ademuri/colordance-circle/hardware/mechanical/pcb-spacer.stl

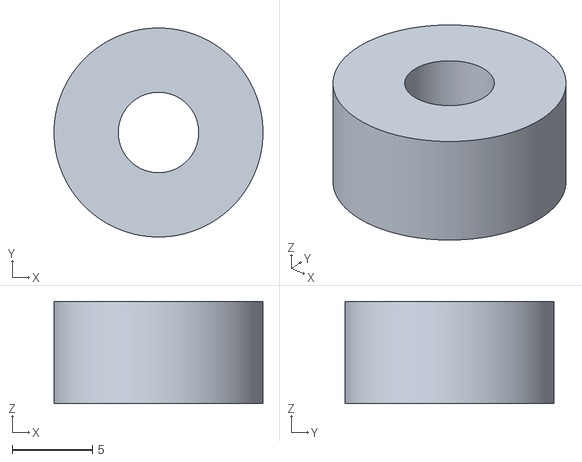
[picture p17: CAD file, 2021-06-12]
hardware/mechanical/pcb-spacer.stl
13.0 x 13.0 x 6.35
