ademuri/colordance-circle/hardware/mechanical/quarter inch washer.stl

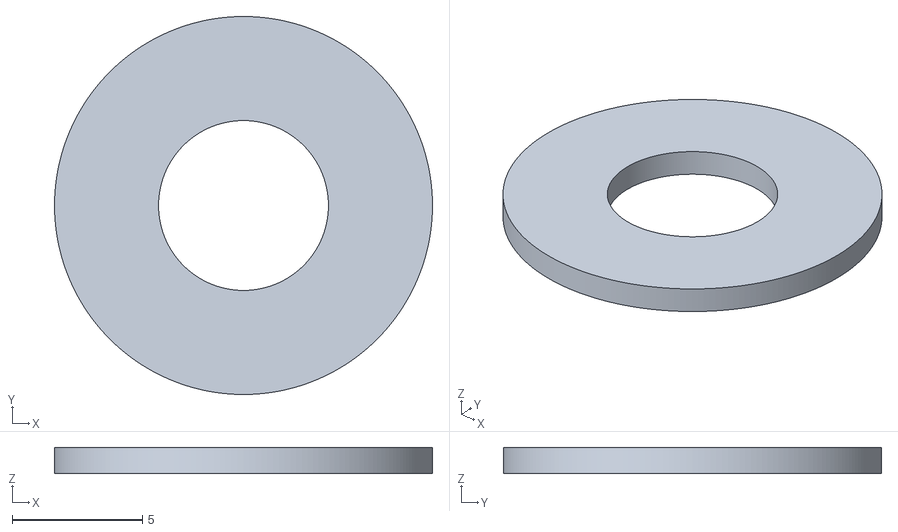
[picture p18: CAD file, 2021-09-08]
hardware/mechanical/quarter inch washer.stl
14.5 x 14.5 x 1.00
