ademuri/colordance-circle/hardware/buttons/circle-small/ref/circle-small.pdf

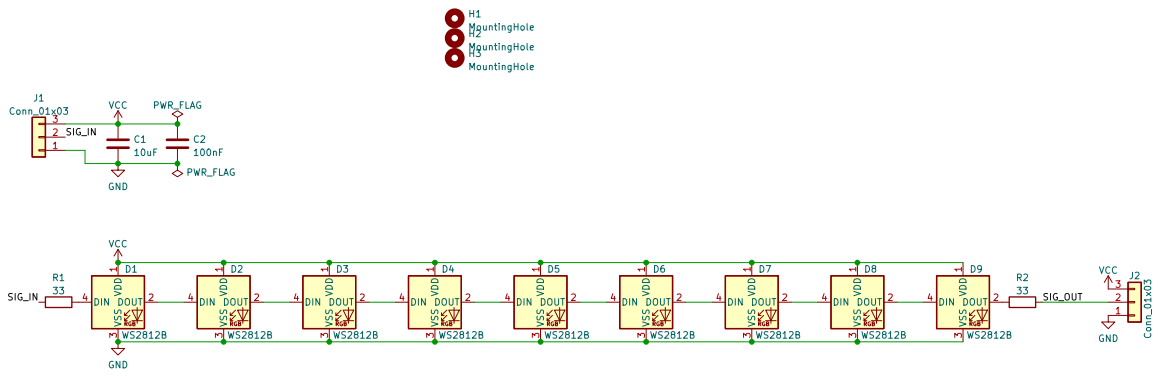
[picture p24: page 1]

File: circle-small.kicad_sch Sheet: /
Id: 1/1 Title:
