ademuri/colordance-circle/hardware/buttons/pot-holder/ref/pot-holder.pdf

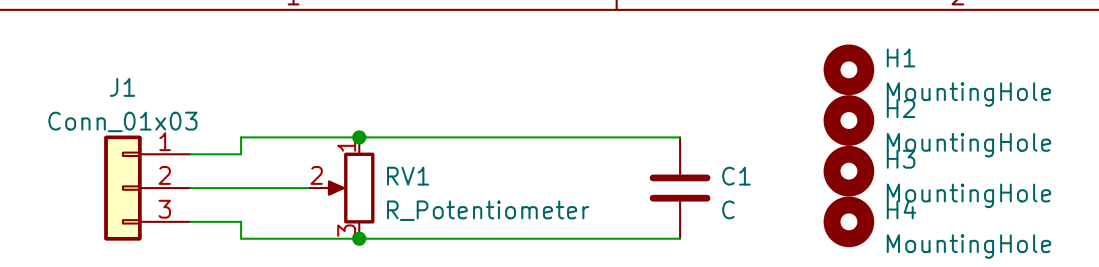
[picture p25: page 1]

File: pot-holder.kicad_sch Sheet: /
Id: 1/1 Title:
