ademuri/colordance-circle/hardware/buttons/circle-small/ref/board_front.pdf

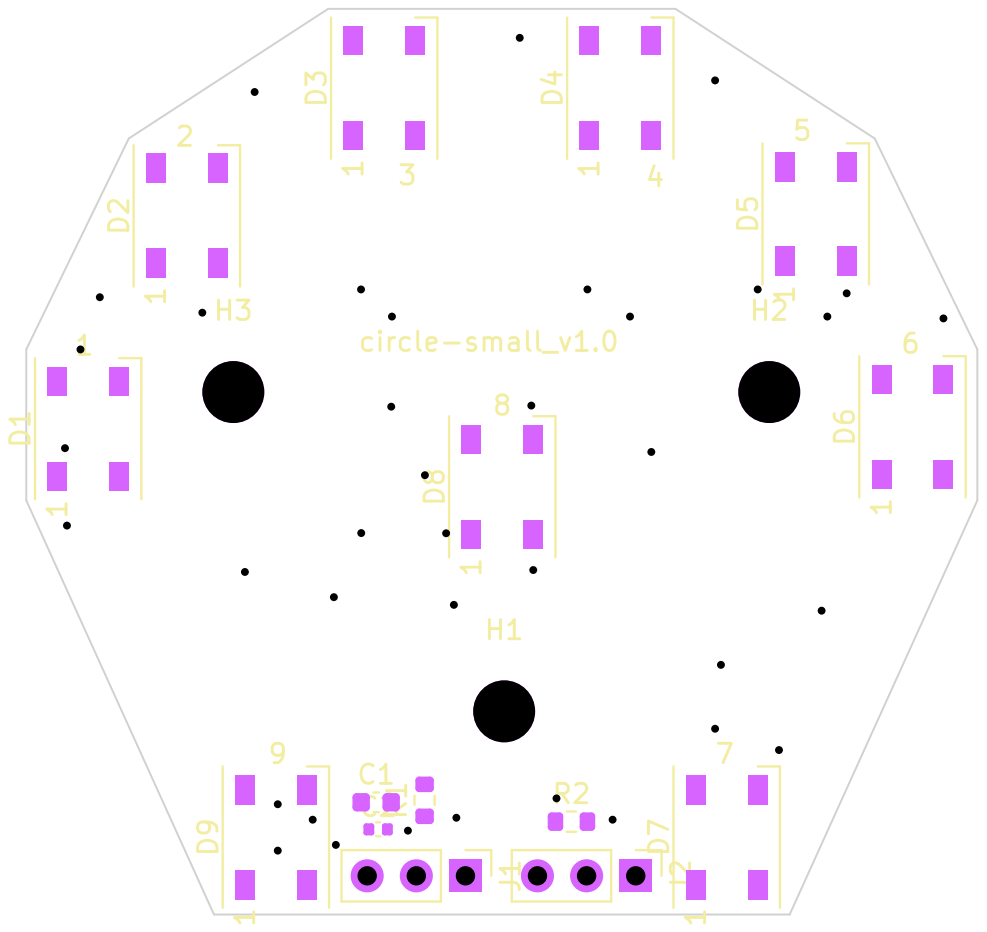
[picture p33: page 1]
