ademuri/colordance-circle/hardware/buttons/heart/ref/board_front.pdf

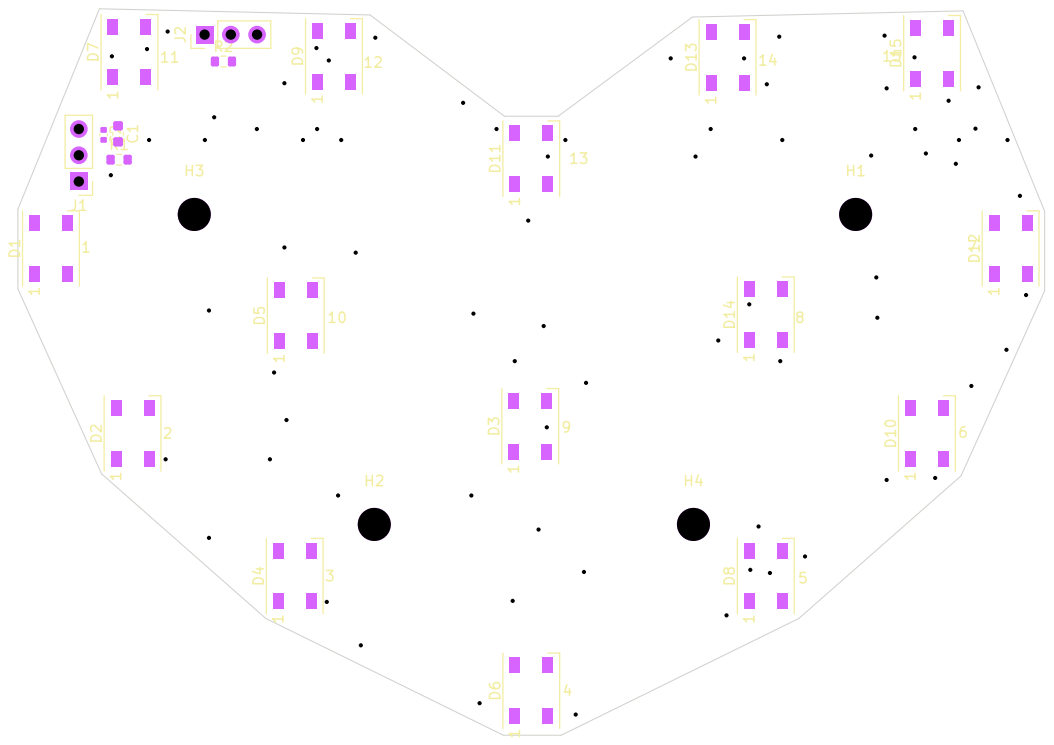
[picture p34: page 1]
