ademuri/colordance-circle/hardware/buttons/heart/ref/heart.pdf

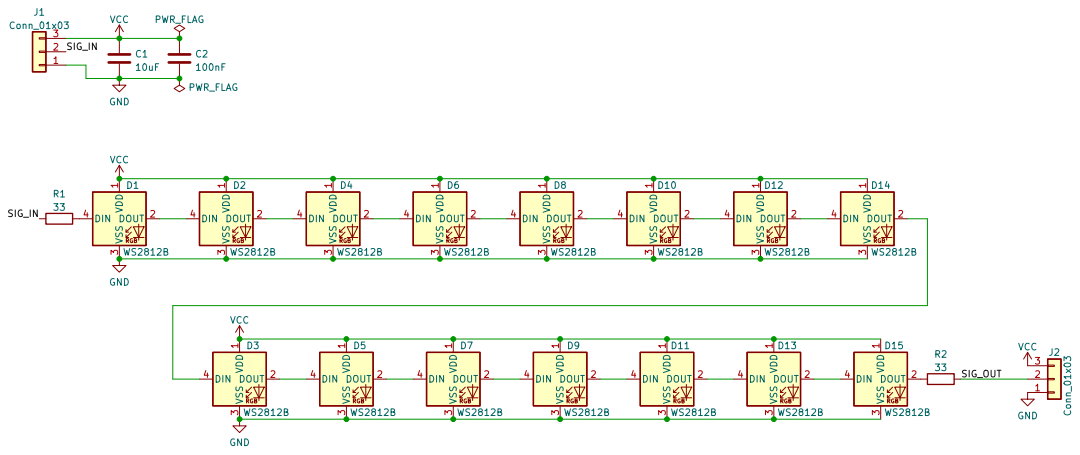
[picture p35: page 1]
