ademuri/colordance-circle/hardware/buttons/slider/ref/slider.pdf

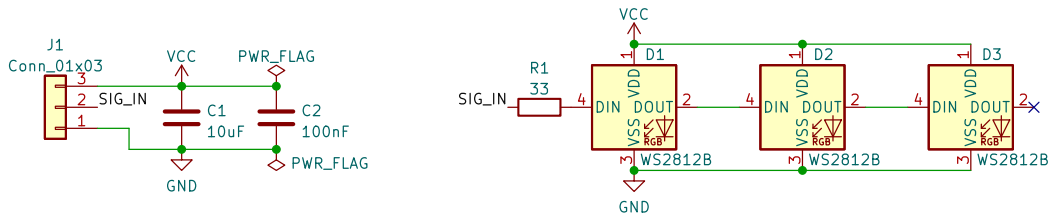
[picture p36: page 1]
