ademuri/colordance-circle/hardware/buttons/square/ref/board_front.pdf

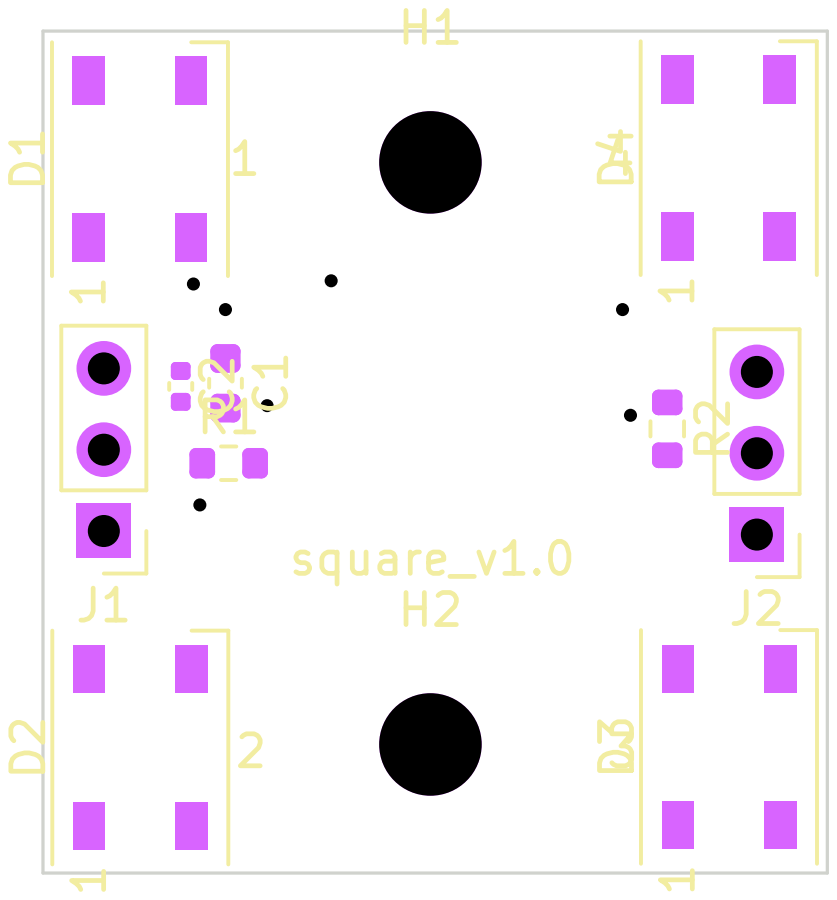
[picture p37: page 1]
