ademuri/colordance-circle/hardware/buttons/square/ref/square.pdf

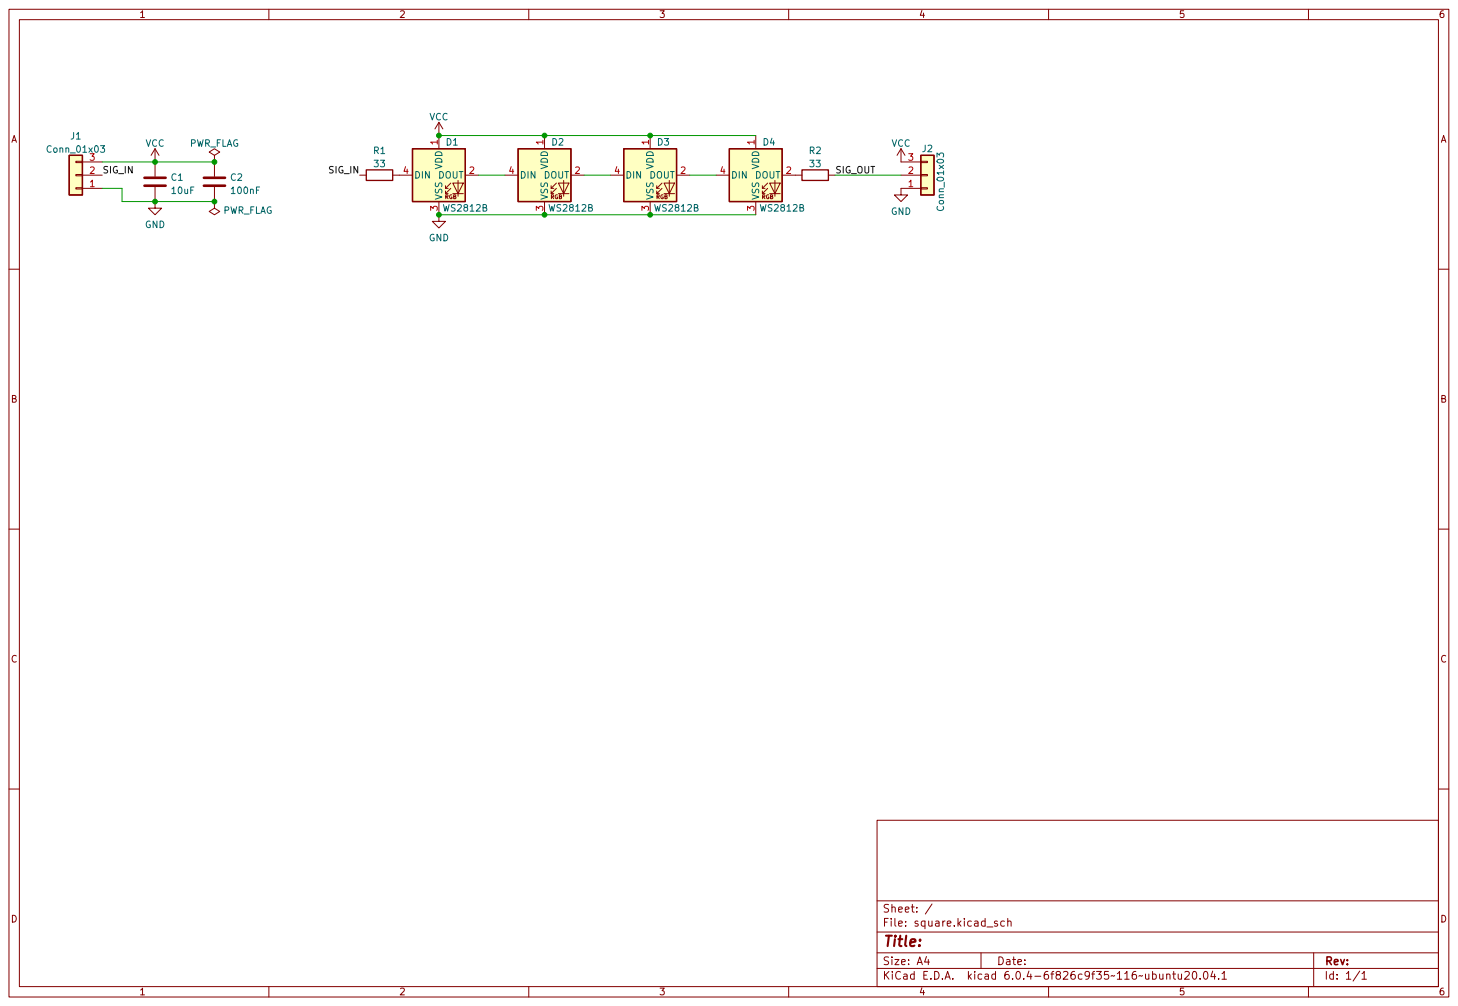
[picture p38: page 1]
