ademuri/colordance-circle/controller/processing_controller/MagicSlider.pde

public class MagicSlider extends MagicControl<Slider> {

  MagicSlider(ControlP5 cp5, String paramIdentifier, String name, int minValue, int maxValue) {
    super(paramIdentifier, cp5.addSlider(name)
      .setRange(minValue, maxValue)
      .setWidth(133)
      .setHeight(50)
      .setHandleSize(20)
      .setSliderMode(Slider.FLEXIBLE));
  }
}
